jnwajei22/carbon-fiber-scale-planes/aircraft/yf-23/photos/cad/bottom/2026-02-14_YF23_BODY-LOWER_SECTION-02_01.png

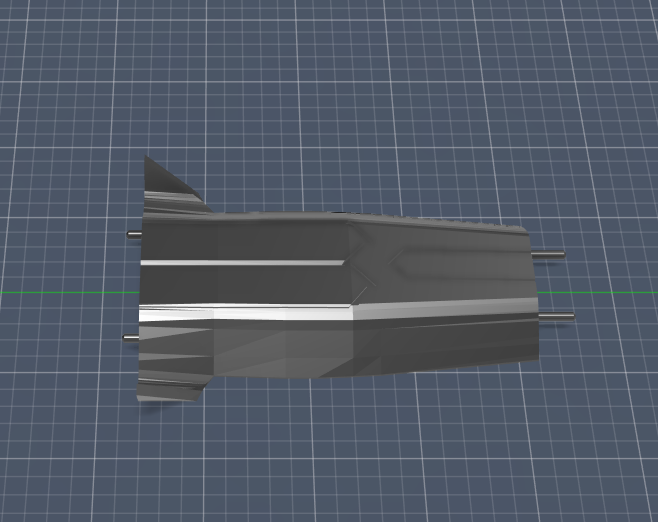
aircraft/yf-23/photos/cad/bottom/2026-02-14_YF23_BODY-LOWER_SECTION-02_01.png
