jnwajei22/carbon-fiber-scale-planes/aircraft/yf-23/photos/cad/bottom/2026-02-14_YF23_BODY-LOWER_SECTION-03_02.png

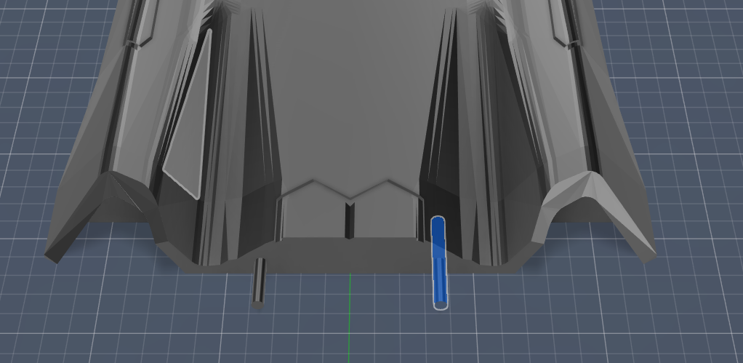
aircraft/yf-23/photos/cad/bottom/2026-02-14_YF23_BODY-LOWER_SECTION-03_02.png
