jnwajei22/carbon-fiber-scale-planes/aircraft/yf-23/photos/cad/top/2026-03-14_YF23_BODY-UPPER_SECTION-01.png

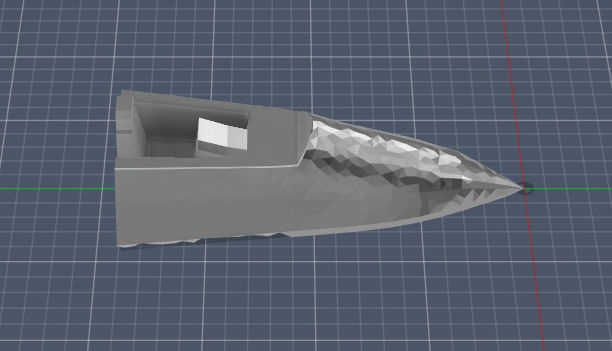
aircraft/yf-23/photos/cad/top/2026-03-14_YF23_BODY-UPPER_SECTION-01.png
