jnwajei22/carbon-fiber-scale-planes/aircraft/yf-23/photos/slicing/bottom/2026-02-26_YF23_BODY-LOWER_SECTION-04_SLICED.png

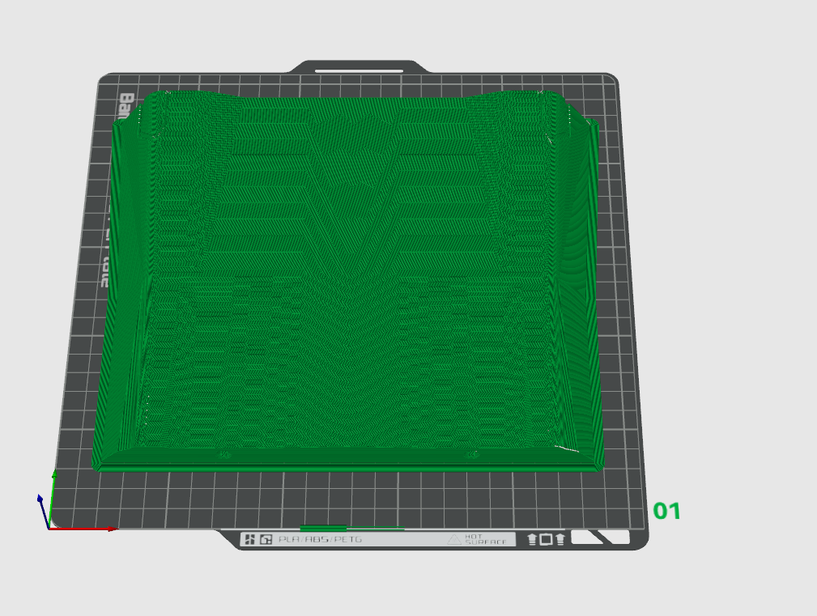
aircraft/yf-23/photos/slicing/bottom/2026-02-26_YF23_BODY-LOWER_SECTION-04_SLICED.png
