jnwajei22/carbon-fiber-scale-planes/aircraft/yf-23/photos/slicing/top/2026-09-05_YF23_BODY-UPPER_CANOPY_SLICED.png.png

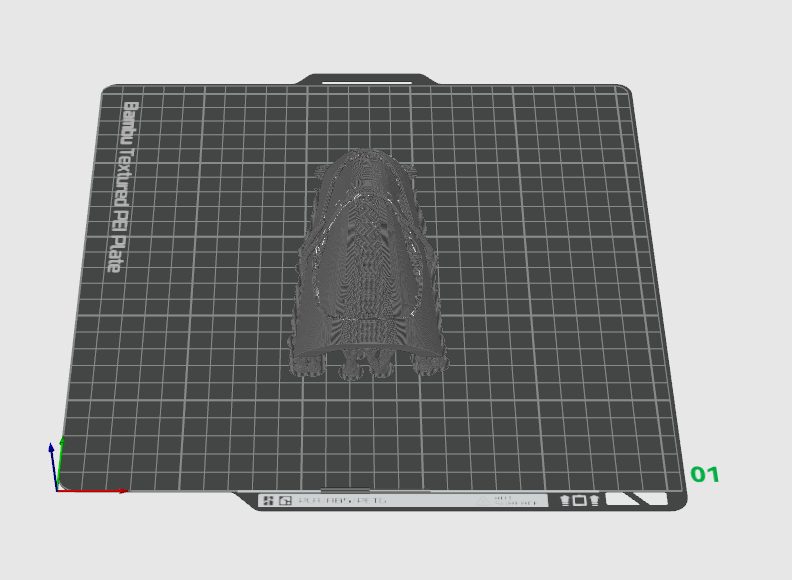
aircraft/yf-23/photos/slicing/top/2026-09-05_YF23_BODY-UPPER_CANOPY_SLICED.png.png
