jnwajei22/carbon-fiber-scale-planes/aircraft/yf-23/photos/slicing/top/2026-09-05_YF23_BODY-UPPER_SECTION-03_C_SLICED.png

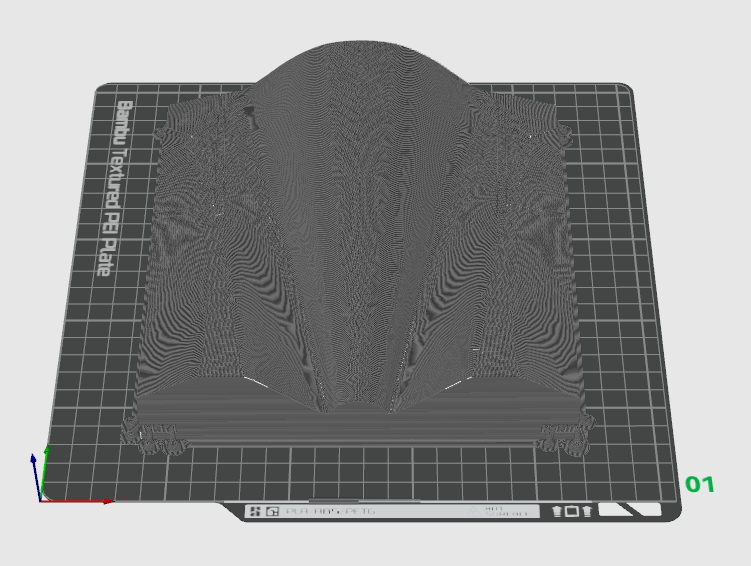
aircraft/yf-23/photos/slicing/top/2026-09-05_YF23_BODY-UPPER_SECTION-03_C_SLICED.png
