jnwajei22/carbon-fiber-scale-planes/aircraft/yf-23/refs/Northrop YF-23 Black Widow II - 3322220/images/1b06e625bf451316475ab049cf89f659.png

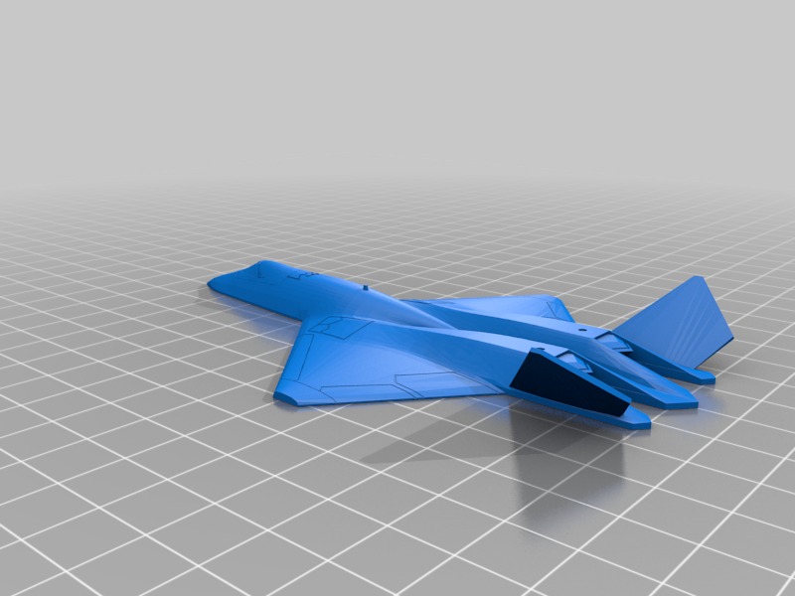
aircraft/yf-23/refs/Northrop YF-23 Black Widow II - 3322220/images/1b06e625bf451316475ab049cf89f659.png
