jnwajei22/carbon-fiber-scale-planes/aircraft/yf-23/refs/Northrop YF-23 Black Widow II - 3322220/images/4fa9f295340049c8137752b571797c91.png

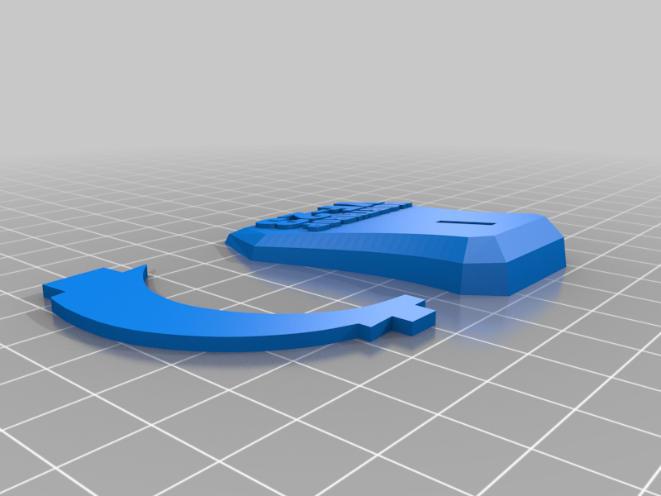
aircraft/yf-23/refs/Northrop YF-23 Black Widow II - 3322220/images/4fa9f295340049c8137752b571797c91.png
