jnwajei22/carbon-fiber-scale-planes/aircraft/yf-23/refs/Northrop YF-23 Black Widow II - 3322220/images/742cefa6ee29ee5b3f25d8faaf2092e0.png

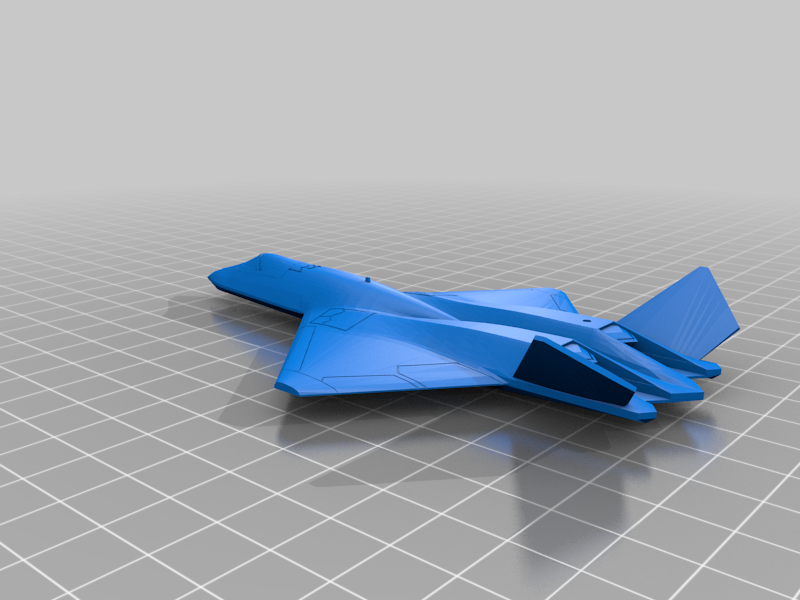
aircraft/yf-23/refs/Northrop YF-23 Black Widow II - 3322220/images/742cefa6ee29ee5b3f25d8faaf2092e0.png
