jnwajei22/carbon-fiber-scale-planes/aircraft/yf-23/refs/Northrop YF-23 Black Widow II - 3322220/images/dbb953969dd4ae01f9b7531742f35c58.png

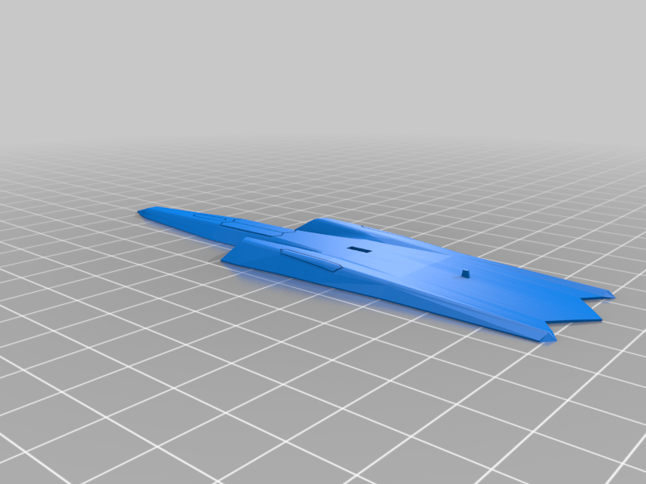
aircraft/yf-23/refs/Northrop YF-23 Black Widow II - 3322220/images/dbb953969dd4ae01f9b7531742f35c58.png
