jnwajei22/carbon-fiber-scale-planes/aircraft/yf-23/refs/Northrop YF-23 Black Widow II - 3322220/images/Screen_Shot_C.jpg

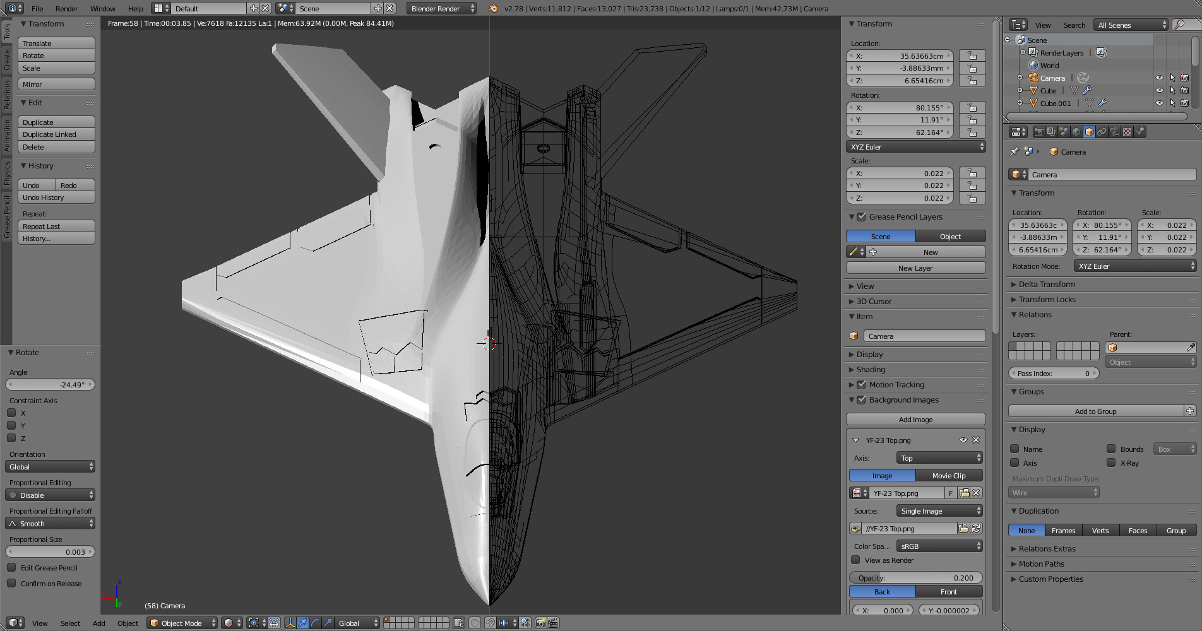
aircraft/yf-23/refs/Northrop YF-23 Black Widow II - 3322220/images/Screen_Shot_C.jpg
