jnwajei22/carbon-fiber-scale-planes/aircraft/yf-23/refs/Northrop YF-23 Black Widow II - 3322220/files/Northrop_YF-23.stl

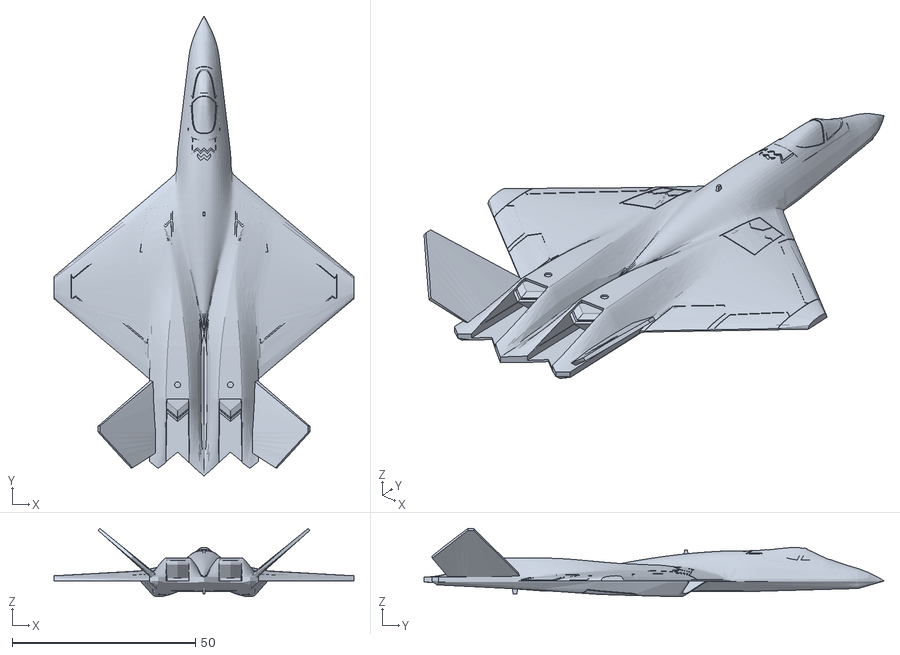
[picture p75: CAD file, 2026-03-07]
aircraft/yf-23/refs/Northrop YF-23 Black Widow II - 3322220/files/Northrop_YF-23.stl
81.9 x 125.5 x 18.6
