jnwajei22/carbon-fiber-scale-planes/aircraft/yf-23/cad/bottom/BODY_LOWER_04.step

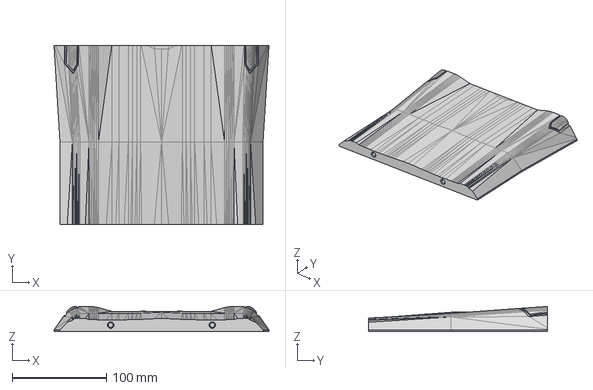
[picture p76: CAD file, 2026-03-07]
aircraft/yf-23/cad/bottom/BODY_LOWER_04.step
228.5 x 190.5 x 26.8 mm
