jnwajei22/carbon-fiber-scale-planes/aircraft/yf-23/cad/top/BODY_UPPER_03_L.step

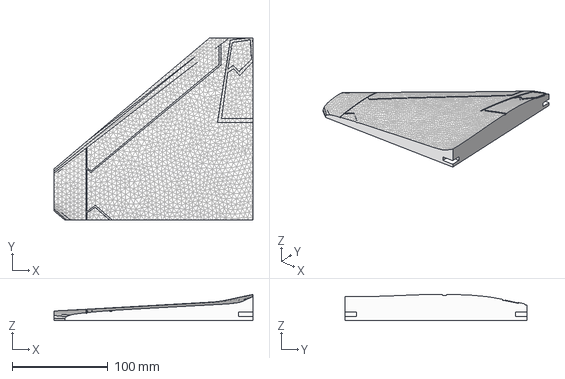
[picture p77: CAD file, 2026-09-06]
aircraft/yf-23/cad/top/BODY_UPPER_03_L.step
208.2 x 190.5 x 27.3 mm
