jnwajei22/carbon-fiber-scale-planes/aircraft/yf-23/cad/bottom/BODY_LOWER_02.step

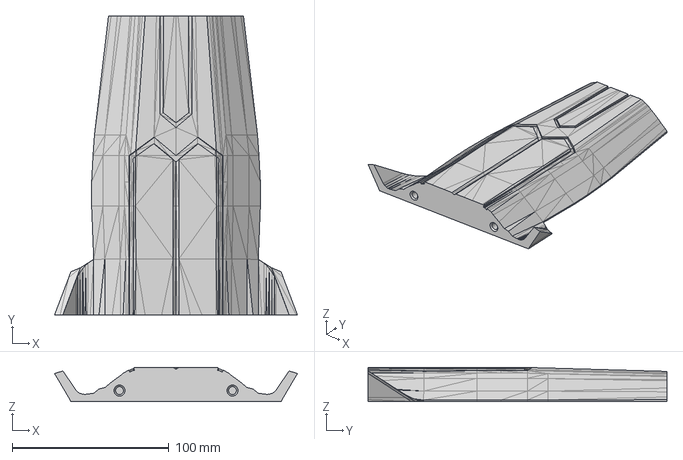
[picture p78: CAD file, 2026-03-07]
aircraft/yf-23/cad/bottom/BODY_LOWER_02.step
154.9 x 190.5 x 21.7 mm
