jnwajei22/carbon-fiber-scale-planes/aircraft/yf-23/cad/top/BODY_UPPER_03_C.step

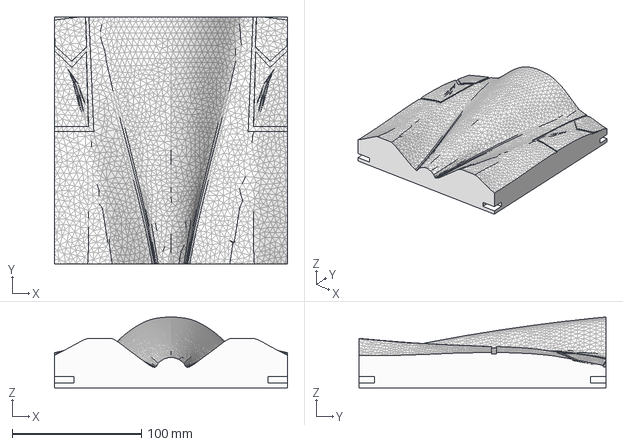
[picture p79: CAD file, 2026-09-06]
aircraft/yf-23/cad/top/BODY_UPPER_03_C.step
180.0 x 190.5 x 54.8 mm
