jnwajei22/carbon-fiber-scale-planes/aircraft/yf-23/cad/top/BODY_UPPER_05_R.step

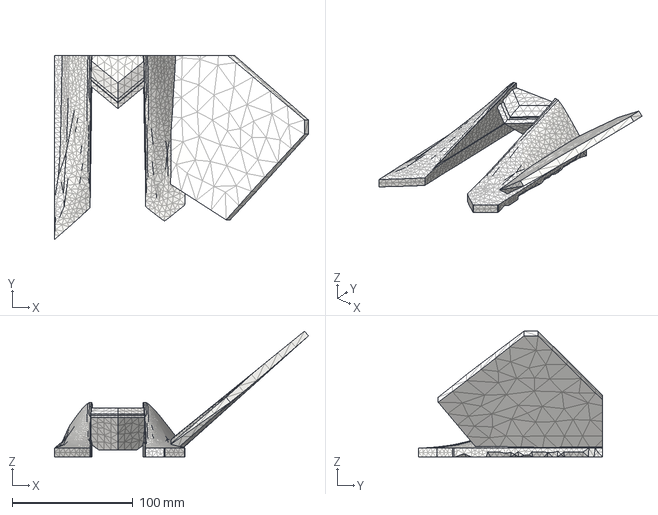
[picture p80: CAD file, 2026-09-06]
aircraft/yf-23/cad/top/BODY_UPPER_05_R.step
210.4 x 152.4 x 104.1 mm
