jnwajei22/carbon-fiber-scale-planes/aircraft/yf-23/cad/top/BODY_UPPER_04_R.step

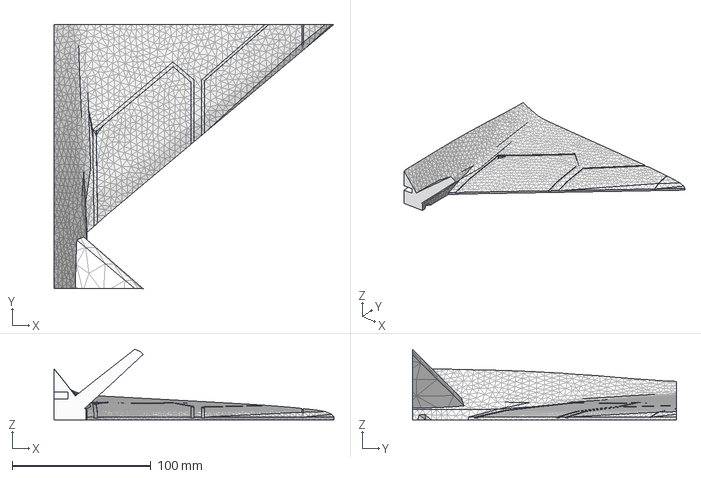
[picture p81: CAD file, 2026-09-06]
aircraft/yf-23/cad/top/BODY_UPPER_04_R.step
201.8 x 190.5 x 51.0 mm
