jnwajei22/carbon-fiber-scale-planes/aircraft/yf-23/cad/top/BODY_UPPER_04_C.step

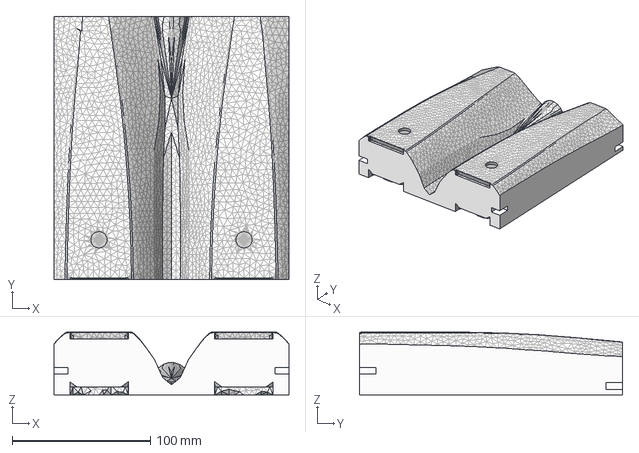
[picture p82: CAD file, 2026-09-06]
aircraft/yf-23/cad/top/BODY_UPPER_04_C.step
170.0 x 190.5 x 45.5 mm
