jnwajei22/carbon-fiber-scale-planes/aircraft/yf-23/cad/top/TAB20.step

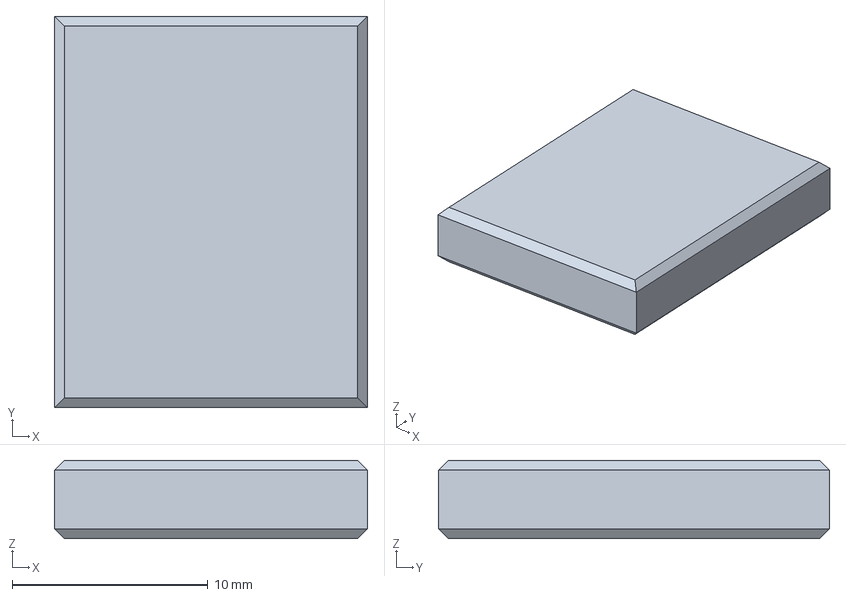
[picture p83: CAD file, 2026-09-06]
aircraft/yf-23/cad/top/TAB20.step
16.0 x 20.0 x 4.00 mm
