jnwajei22/carbon-fiber-scale-planes/aircraft/yf-23/photos/prints/2026-02-28_YF23-4.JPEG

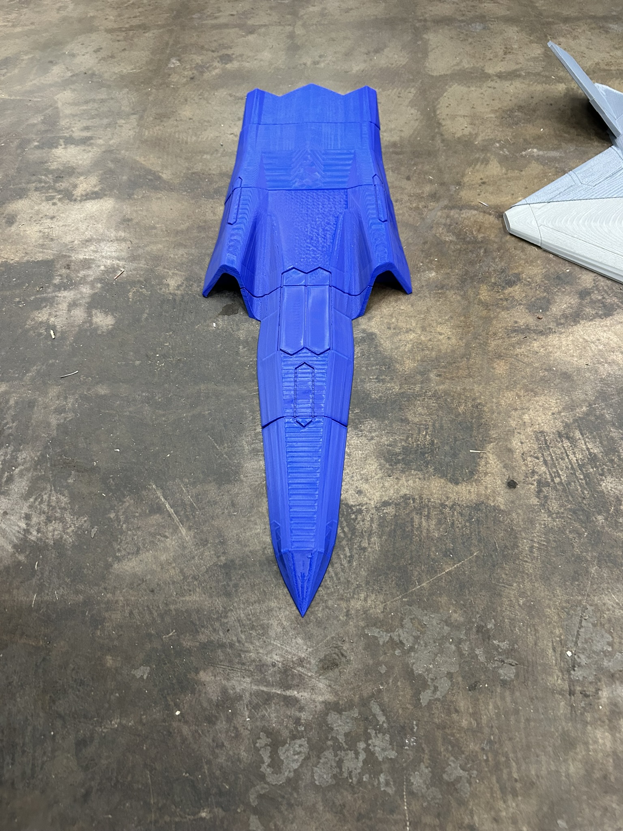
aircraft/yf-23/photos/prints/2026-02-28_YF23-4.JPEG
