jnwajei22/carbon-fiber-scale-planes/aircraft/yf-23/photos/prints/top/2026-02-28_YF23_BODY-UPPER-1.JPEG

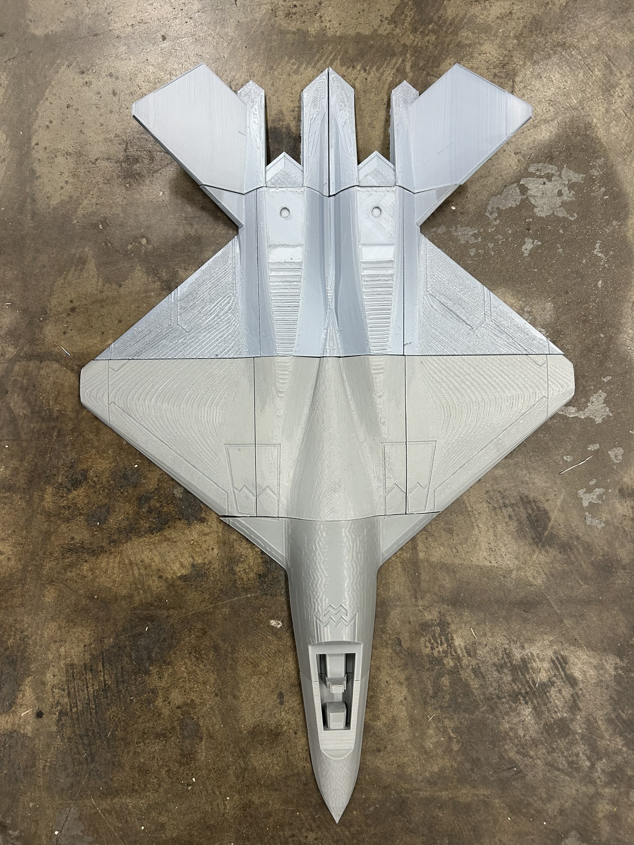
aircraft/yf-23/photos/prints/top/2026-02-28_YF23_BODY-UPPER-1.JPEG
