jnwajei22/carbon-fiber-scale-planes/aircraft/yf-23/photos/prints/top/2026-09-05_YF23_BODY-UPPER_SECTION-04_L.JPEG

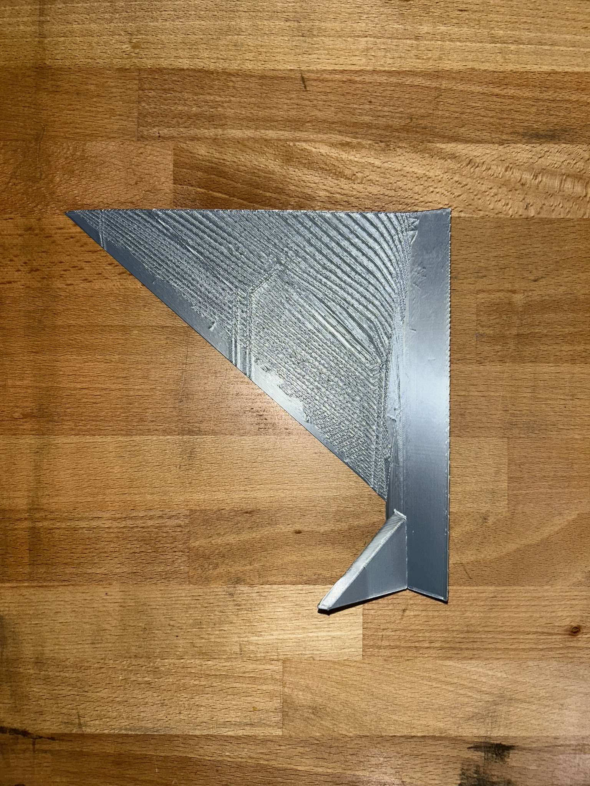
aircraft/yf-23/photos/prints/top/2026-09-05_YF23_BODY-UPPER_SECTION-04_L.JPEG
