jnwajei22/carbon-fiber-scale-planes/aircraft/yf-23/photos/prints/test-coupons/bottom/BODY_LOWER_TEST_COUPON.JPEG

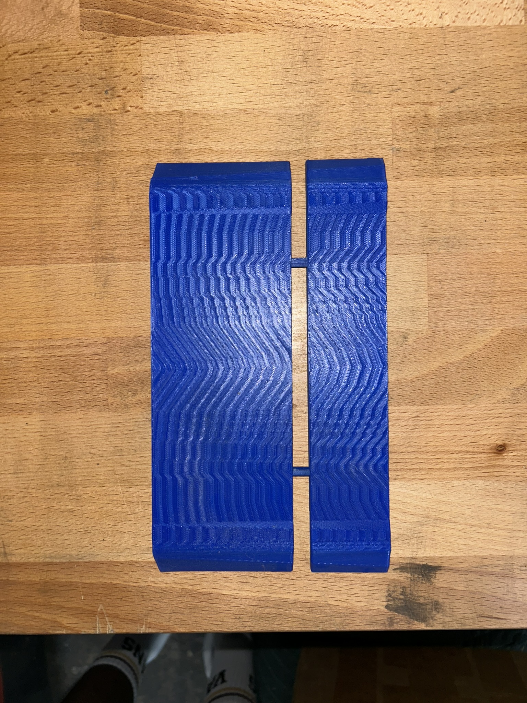
aircraft/yf-23/photos/prints/test-coupons/bottom/BODY_LOWER_TEST_COUPON.JPEG
