jnwajei22/carbon-fiber-scale-planes/aircraft/yf-23/photos/prints/bottom/2026-02-28_YF23_BODY-LOWER_SECTION-03.jpeg

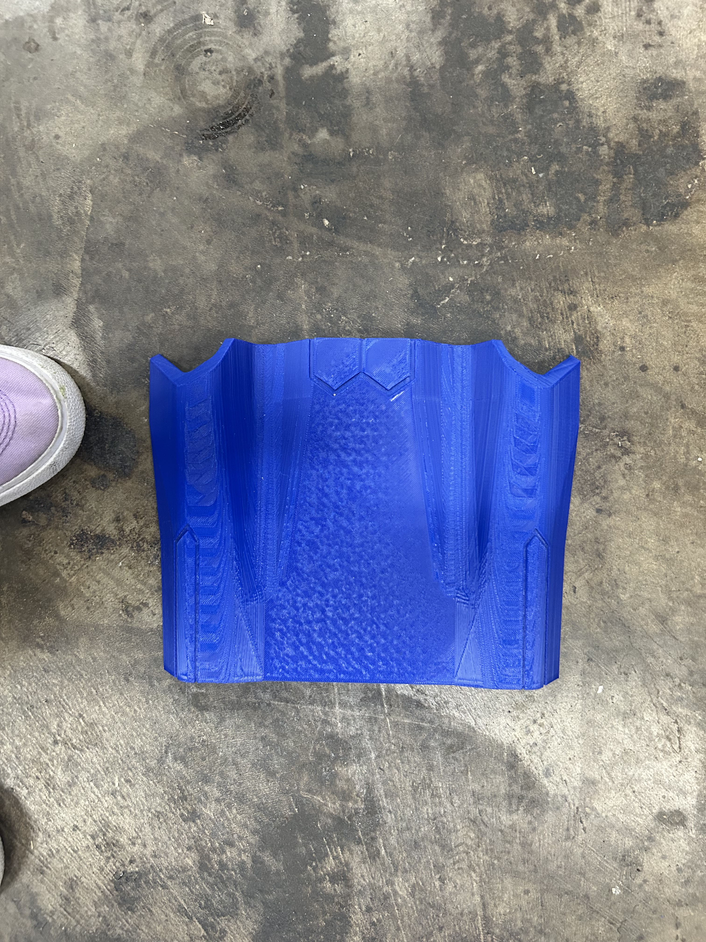
aircraft/yf-23/photos/prints/bottom/2026-02-28_YF23_BODY-LOWER_SECTION-03.jpeg
